teuler/hexbotling/pictures/body_frame.png

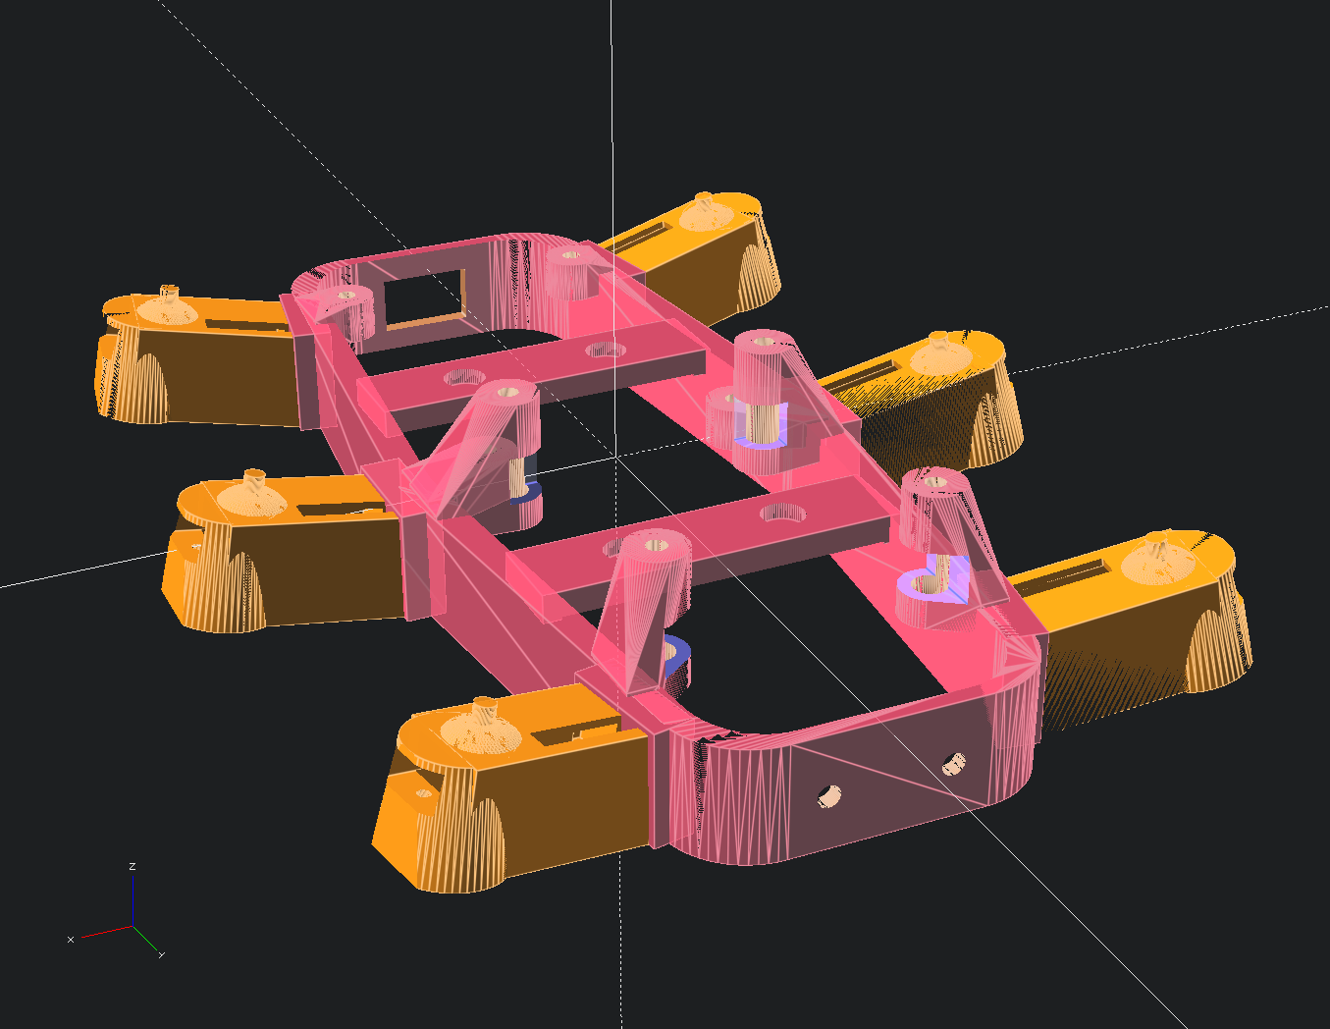
pictures/body_frame.png
