teuler/hexbotling/pictures/body_frame_wbothboards.png

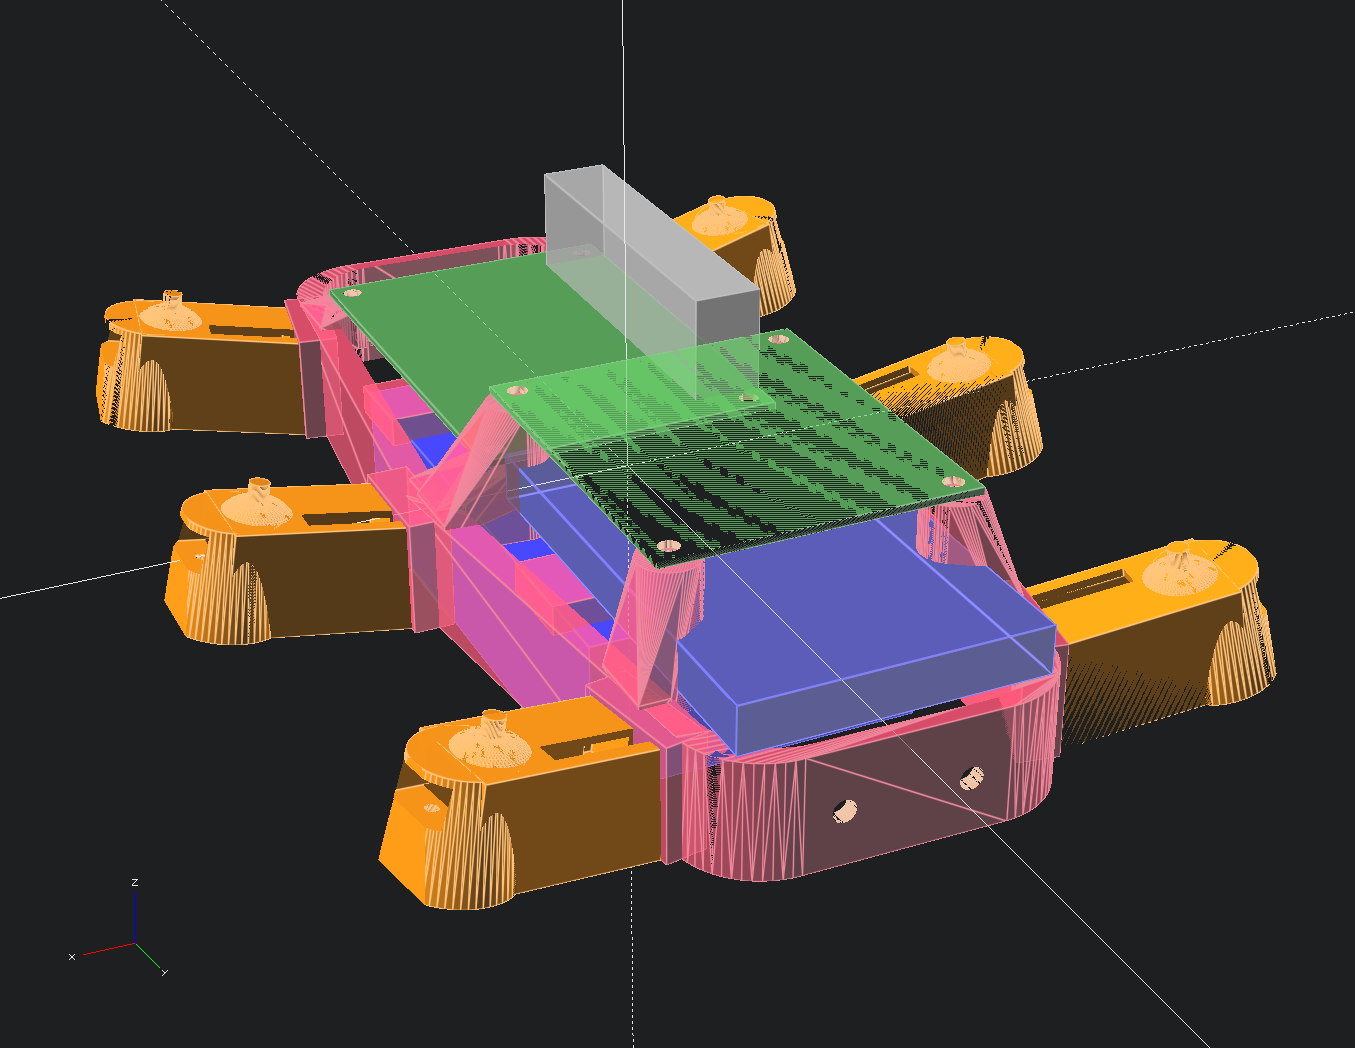
pictures/body_frame_wbothboards.png
