teuler/hexbotling/pictures/complete.png

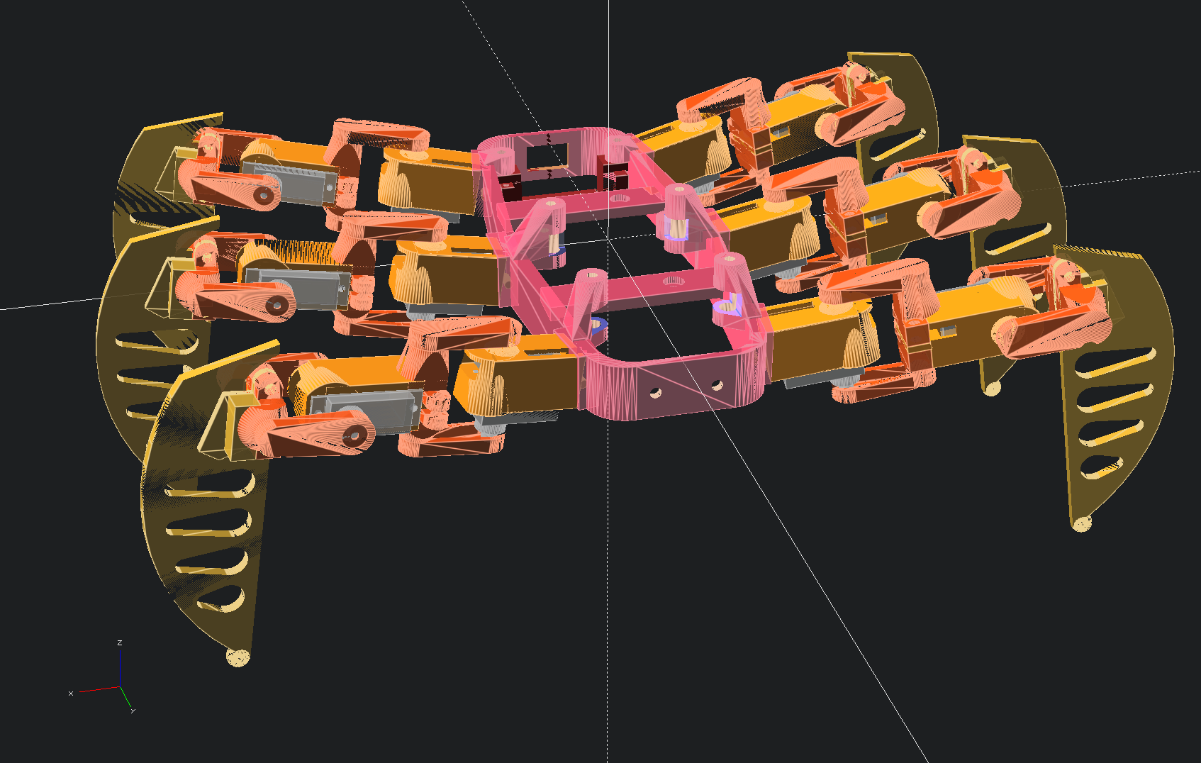
pictures/complete.png
