teuler/hexbotling/pictures/complete_alt_top.png

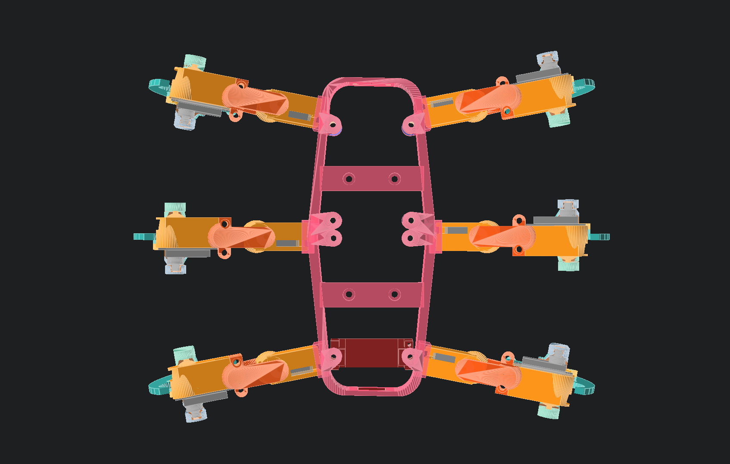
pictures/complete_alt_top.png
