teuler/hexbotling/pictures/complete_alt_top_wb.png

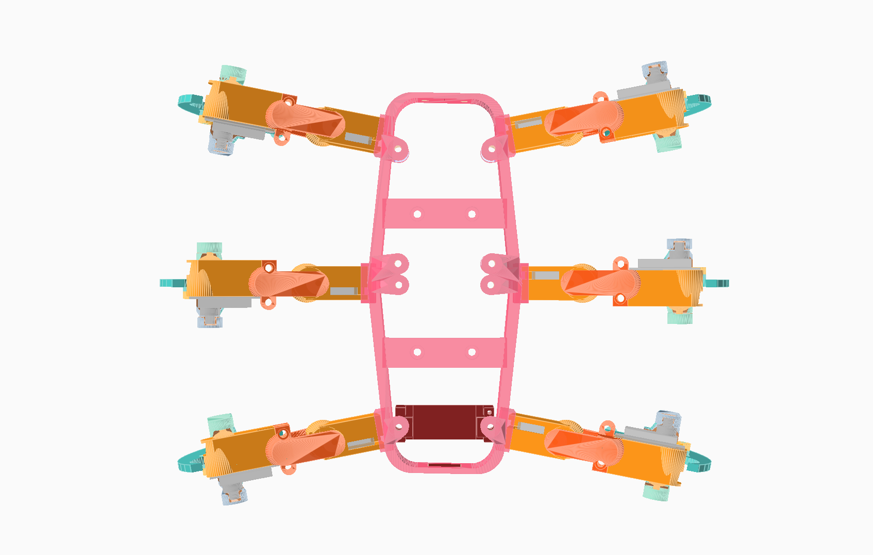
pictures/complete_alt_top_wb.png
