teuler/hexbotling/pictures/complete_alternative legs.png

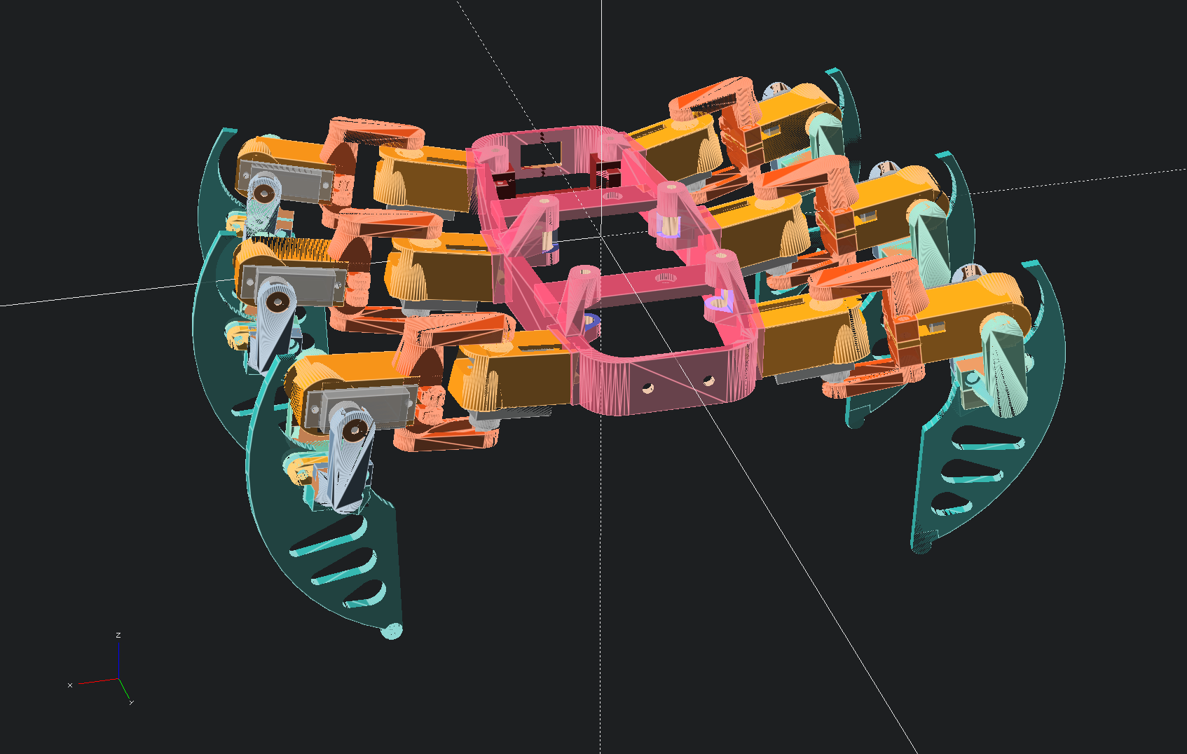
pictures/complete_alternative legs.png
