teuler/hexbotling/pictures/complete_different_legs.png

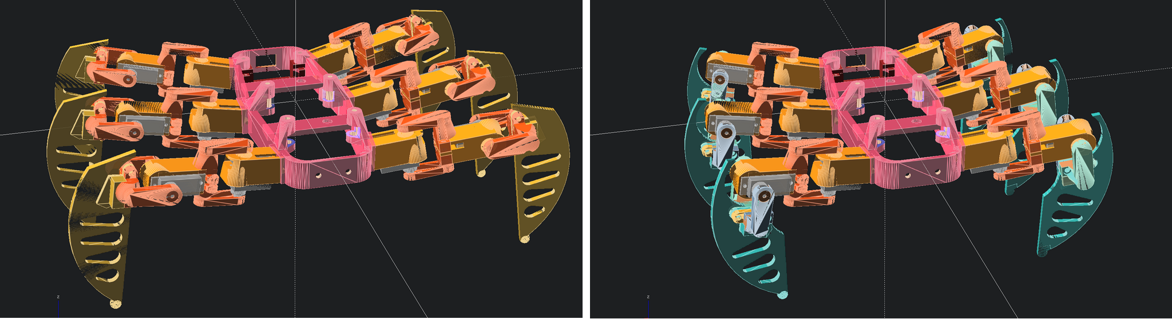
pictures/complete_different_legs.png
