teuler/hexbotling/pictures/IMG_8886.jpg

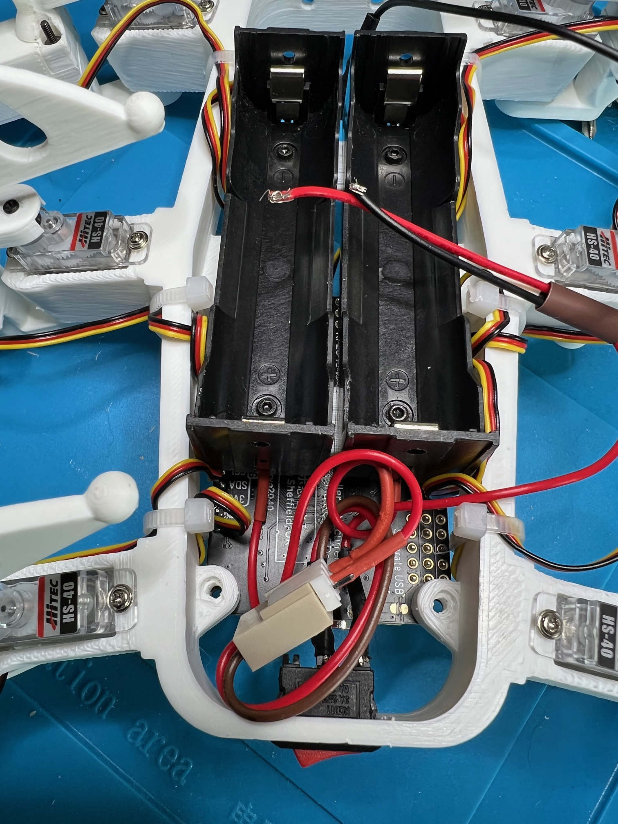
pictures/IMG_8886.jpg
