teuler/hexbotling/pictures/IMG_8889.jpg

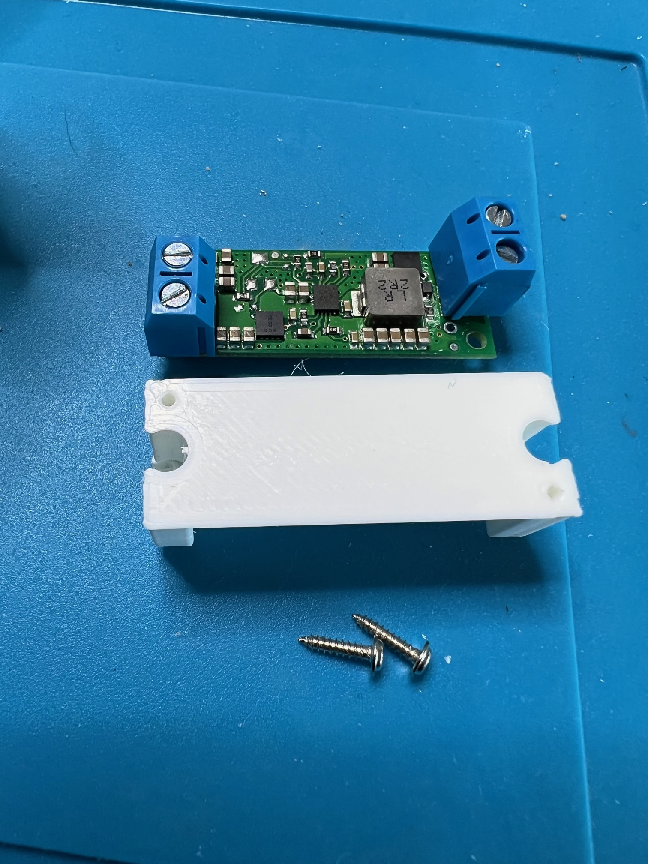
pictures/IMG_8889.jpg
