teuler/hexbotling/pictures/IMG_8890.jpg

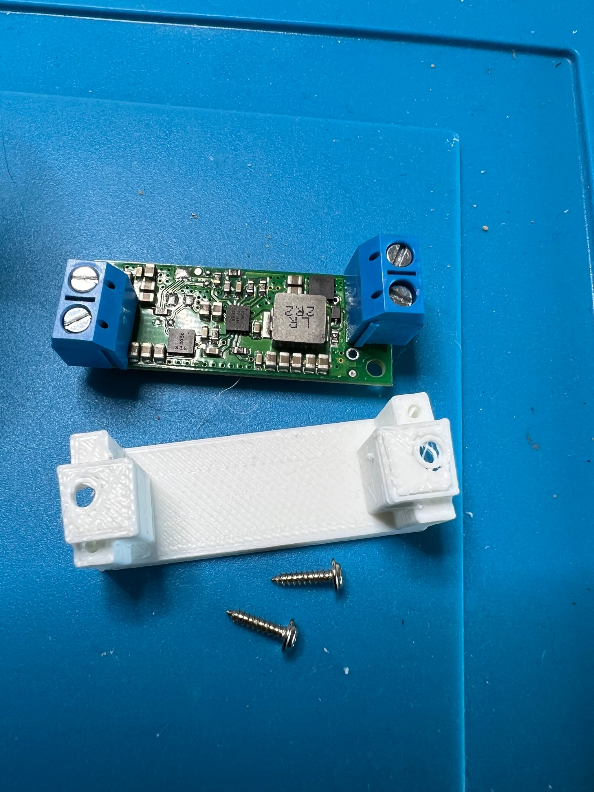
pictures/IMG_8890.jpg
