teuler/hexbotling/pictures/IMG_8891.jpg

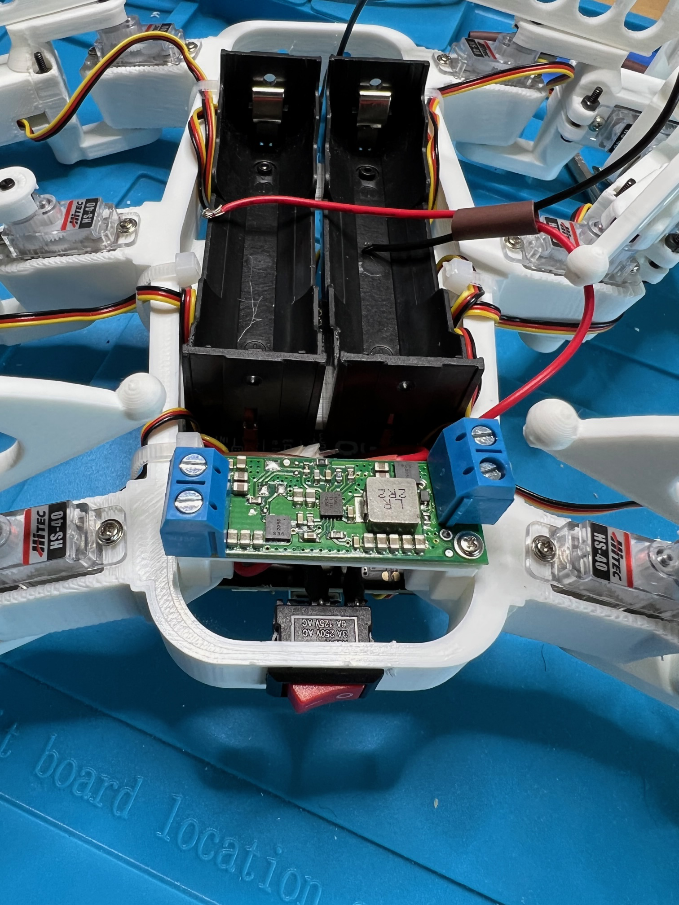
pictures/IMG_8891.jpg
