teuler/hexbotling/pictures/IMG_8892.jpg

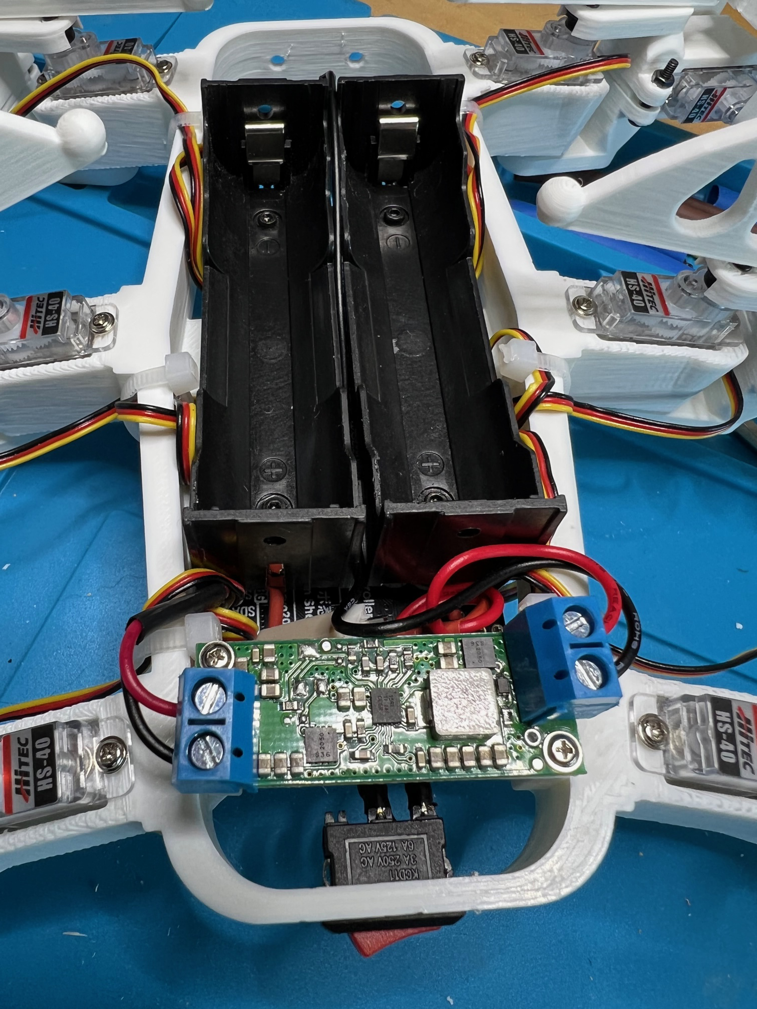
pictures/IMG_8892.jpg
