teuler/hexbotling/pictures/leg_1.png

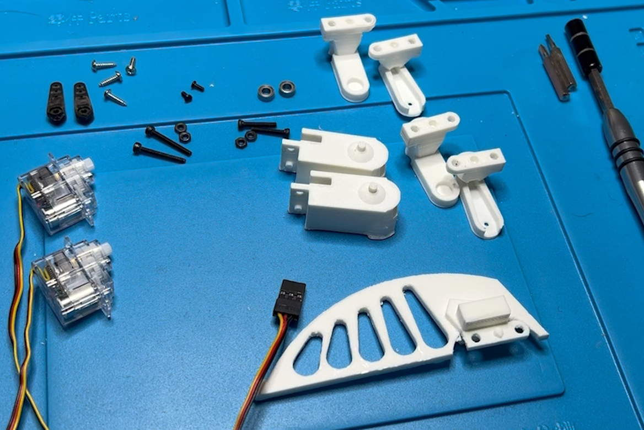
pictures/leg_1.png
