teuler/hexbotling/pictures/leg_1_wLabels.png

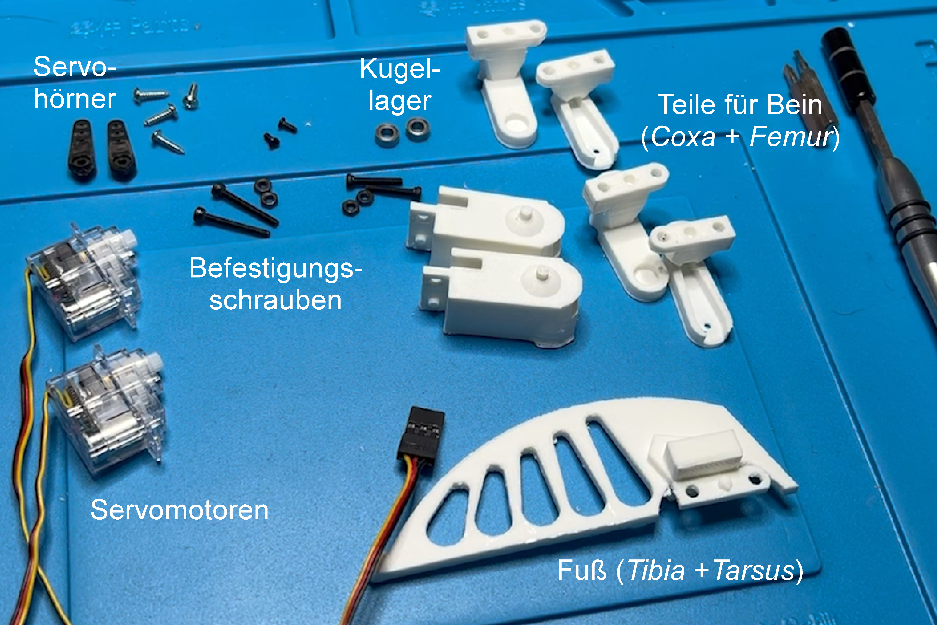
pictures/leg_1_wLabels.png
