teuler/hexbotling/pictures/leg_2.png

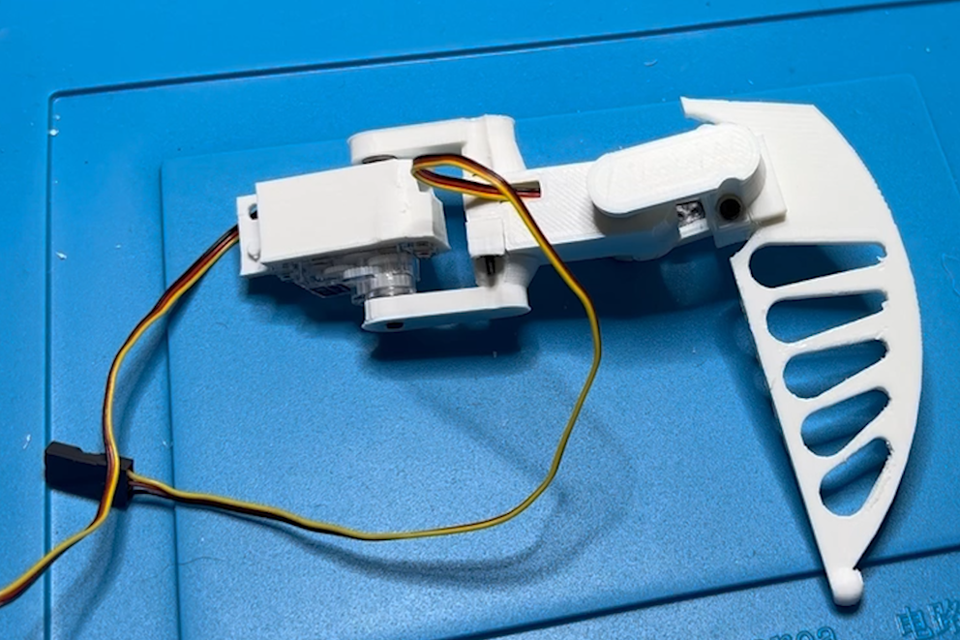
pictures/leg_2.png
