teuler/hexbotling/pictures/leg_3.png

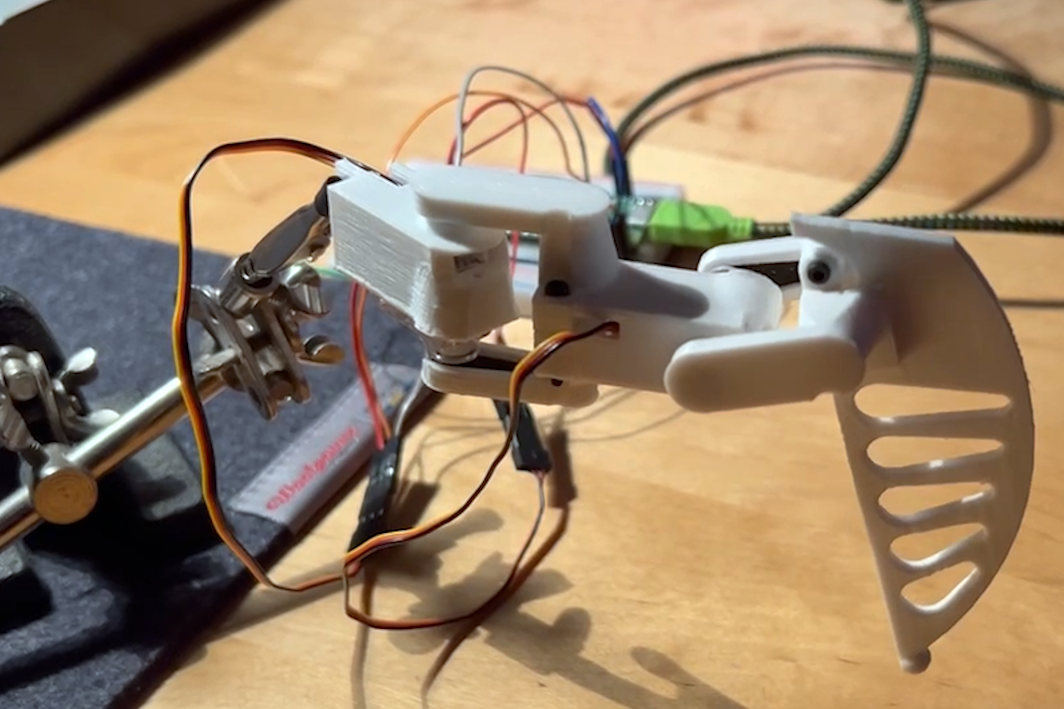
pictures/leg_3.png
