teuler/hexbotling/pictures/leg_comparison.png

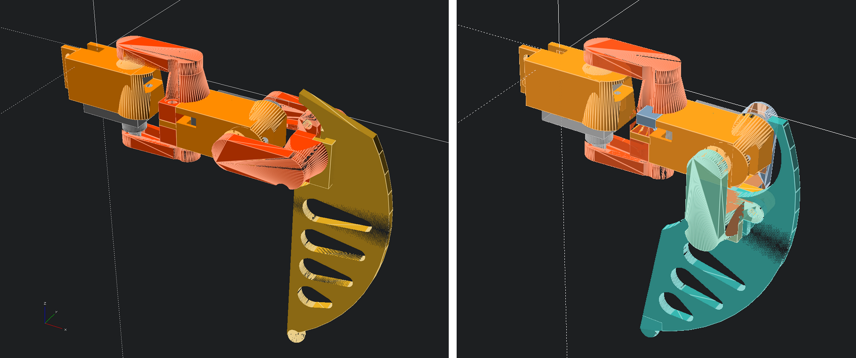
pictures/leg_comparison.png
