teuler/hexbotling/pictures/scad_1.png

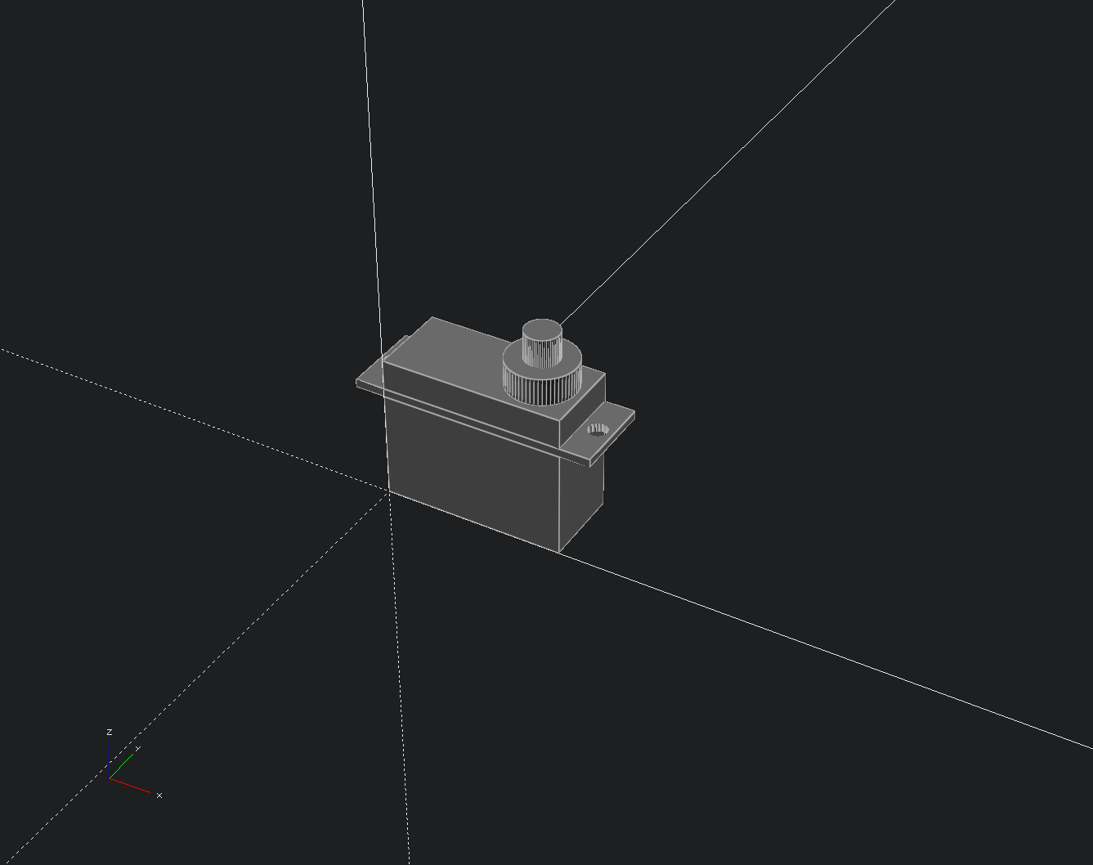
pictures/scad_1.png
