teuler/hexbotling/pictures/scad_3.png

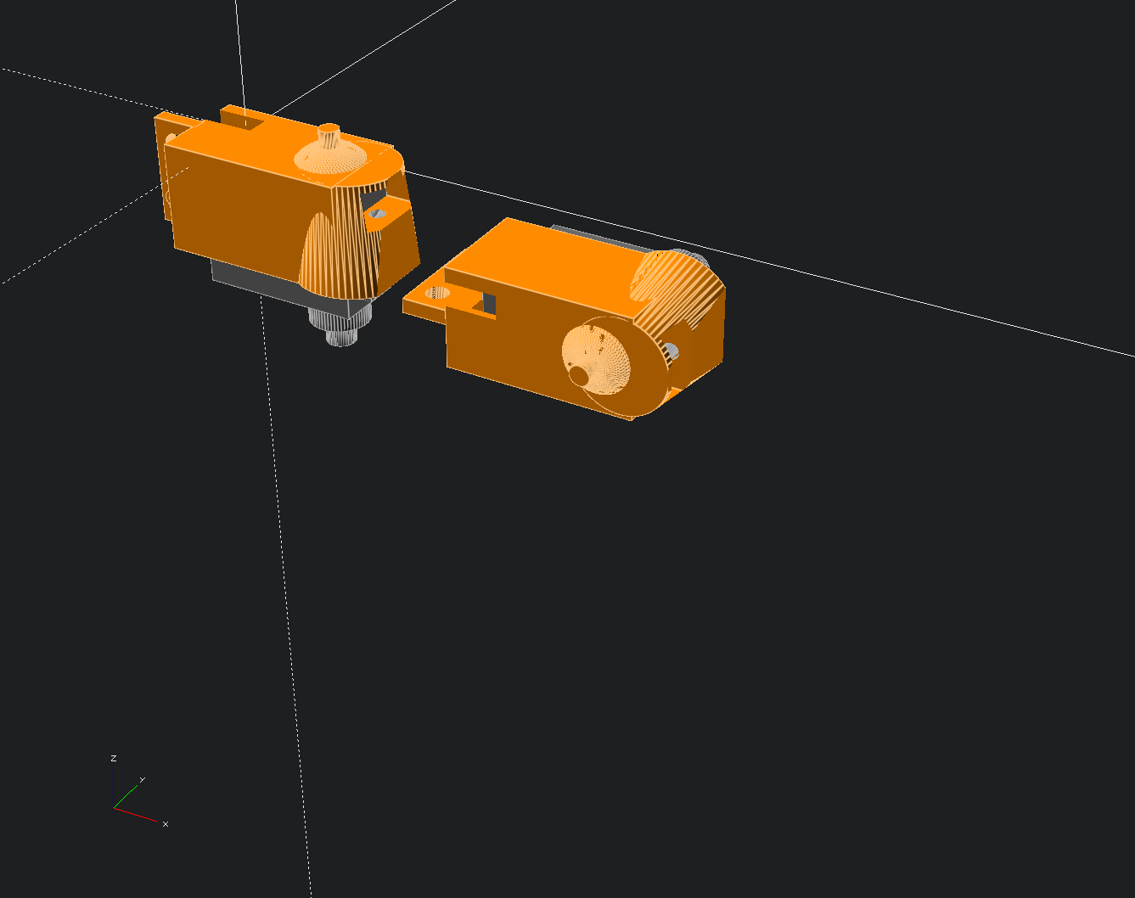
pictures/scad_3.png
