teuler/hexbotling/pictures/scad_4.png

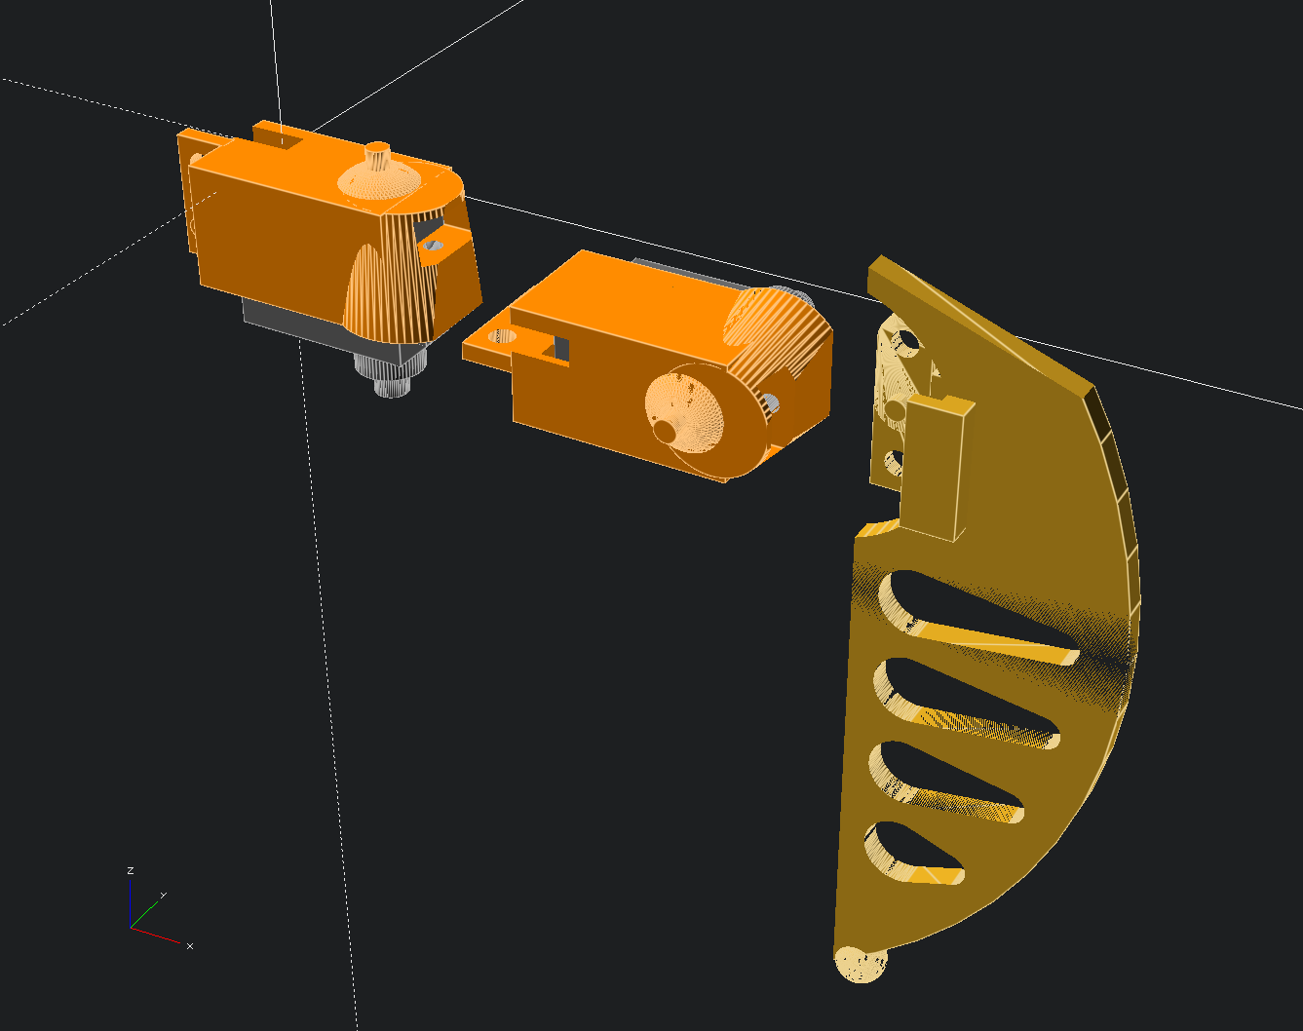
pictures/scad_4.png
