teuler/hexbotling/pictures/scad_5.png

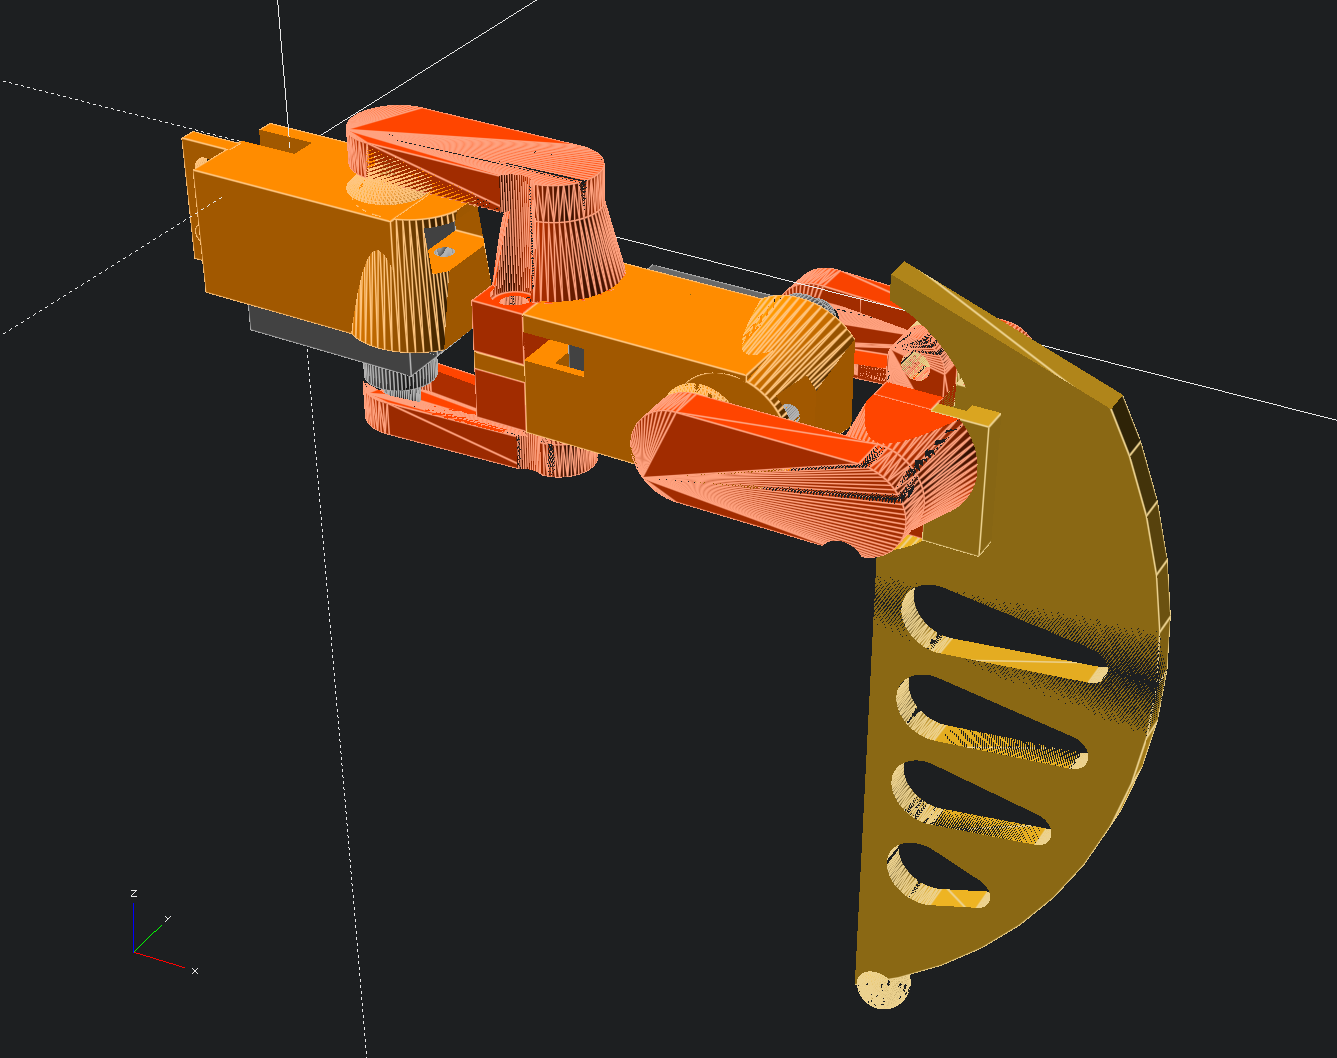
pictures/scad_5.png
