teuler/hexbotling/pictures/scad_5a.png

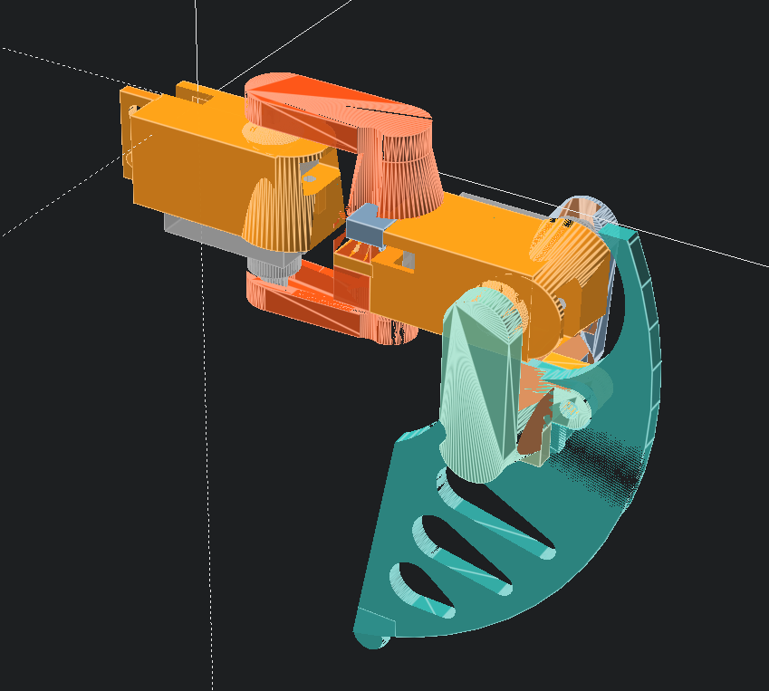
pictures/scad_5a.png
