teuler/hexbotling/pictures/servo_power.png

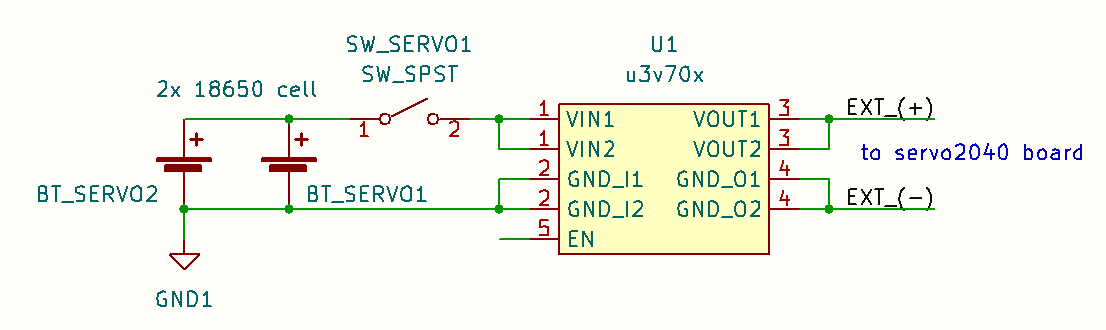
pictures/servo_power.png
