teuler/hexbotling/pictures/video_part_1_tn.png

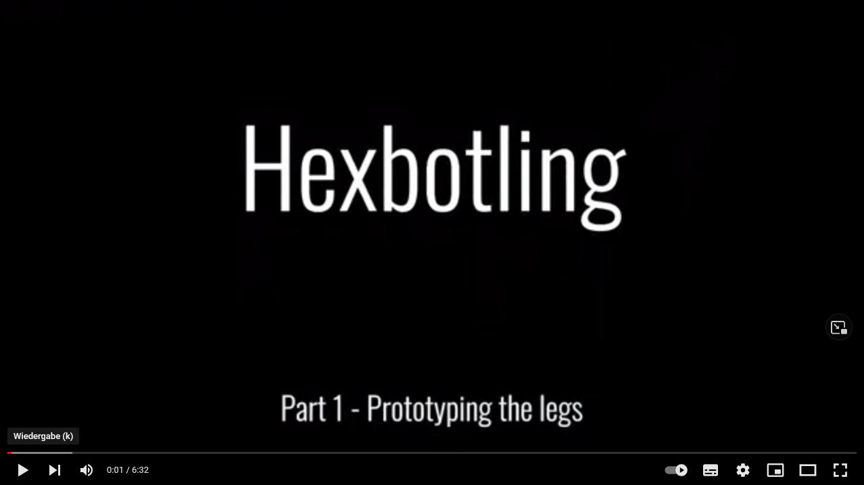
pictures/video_part_1_tn.png
