teuler/hexbotling/pictures/voltage_converter_holder_1.png

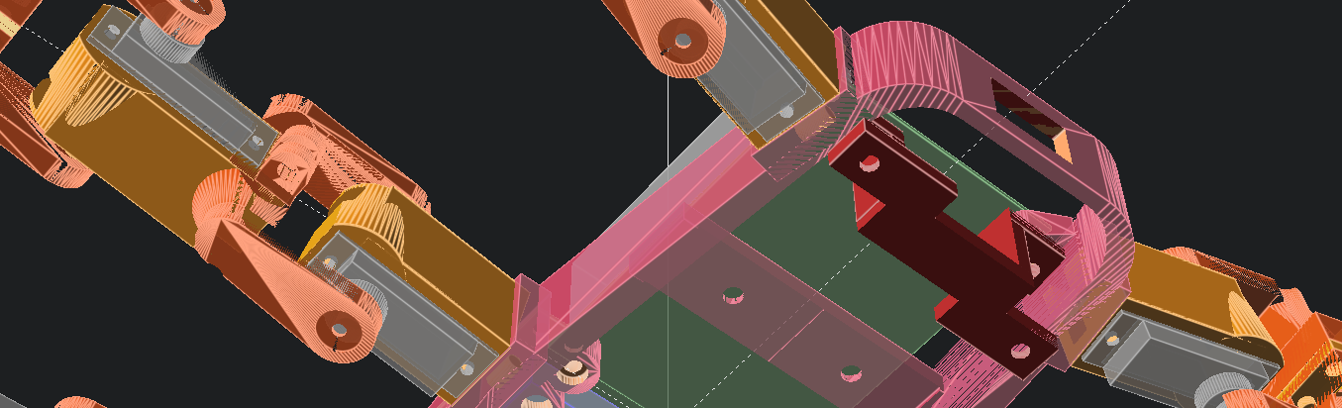
pictures/voltage_converter_holder_1.png
