teuler/hexbotling/pictures/setup_remote_version_2.png

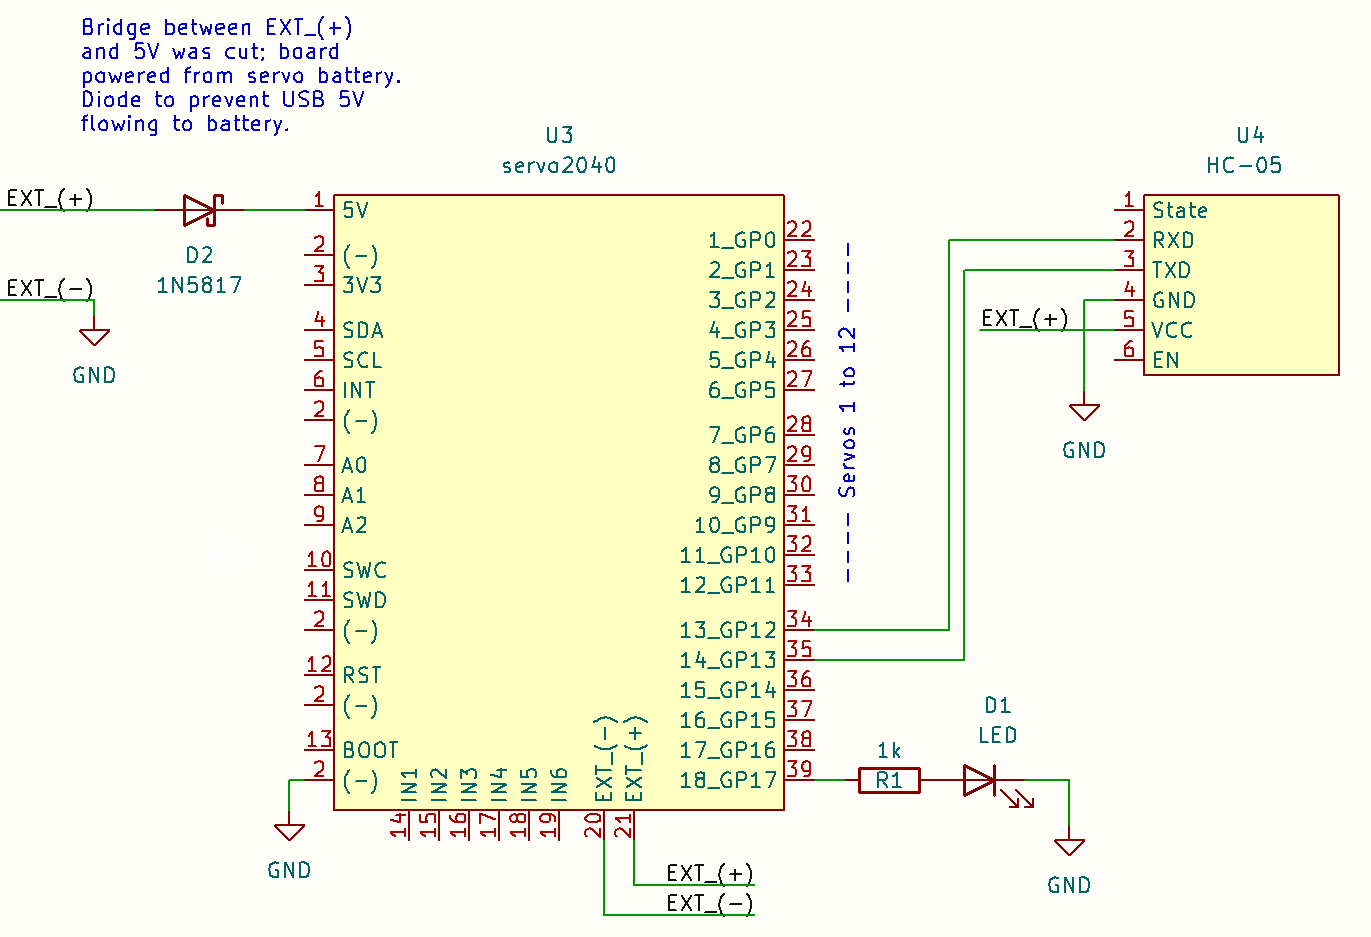
pictures/setup_remote_version_2.png
